cacheworks/Wubbo/KiCad/3d/HRO  TYPE-C-31-M-12.step

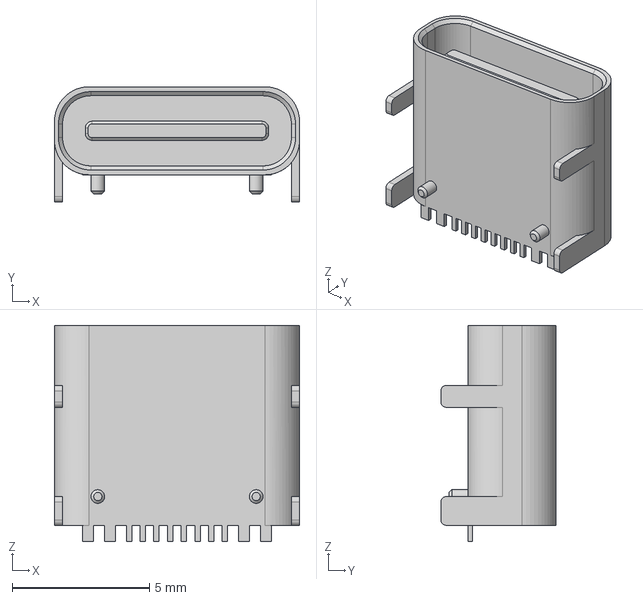
[picture p18: CAD file, 2022-01-12]
KiCad/3d/HRO TYPE-C-31-M-12.step
8.94 x 4.21 x 7.90 mm
