cacheworks/Wubbo/KiCad/3d/USB-C-C168688.step

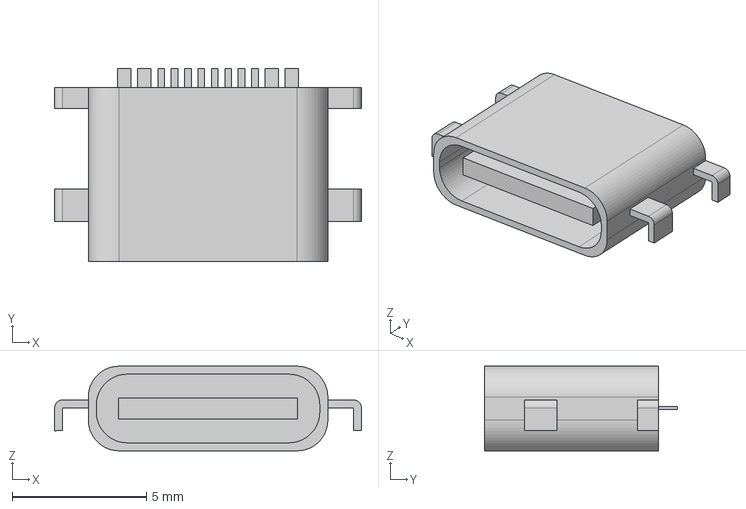
[picture p19: CAD file, 2022-01-12]
KiCad/3d/USB-C-C168688.step
11.5 x 7.20 x 3.16 mm
