cacheworks/Wubbo/KiCad/3d/PG1350-socket.STEP

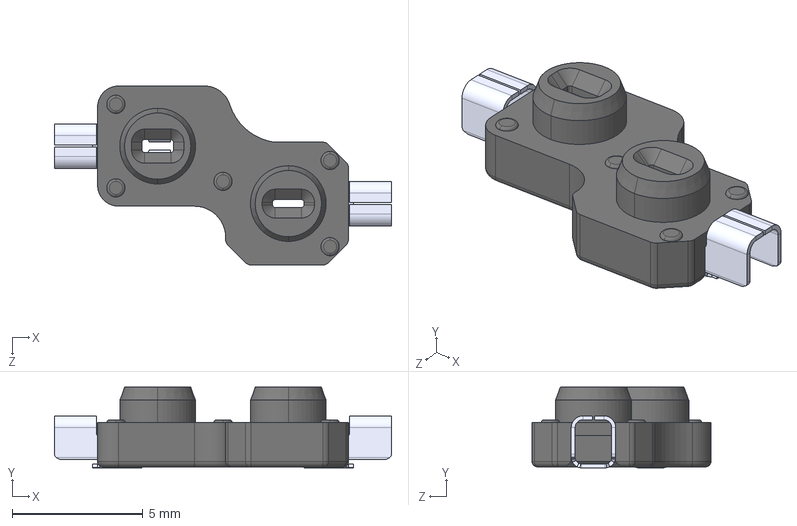
[picture p20: CAD file, 2022-01-12]
KiCad/3d/PG1350-socket.STEP
12.9 x 3.09 x 6.85 mm
pin x 2
socket
