cacheworks/Wubbo/KiCad/3d/LED_SK6812MINI-E.step

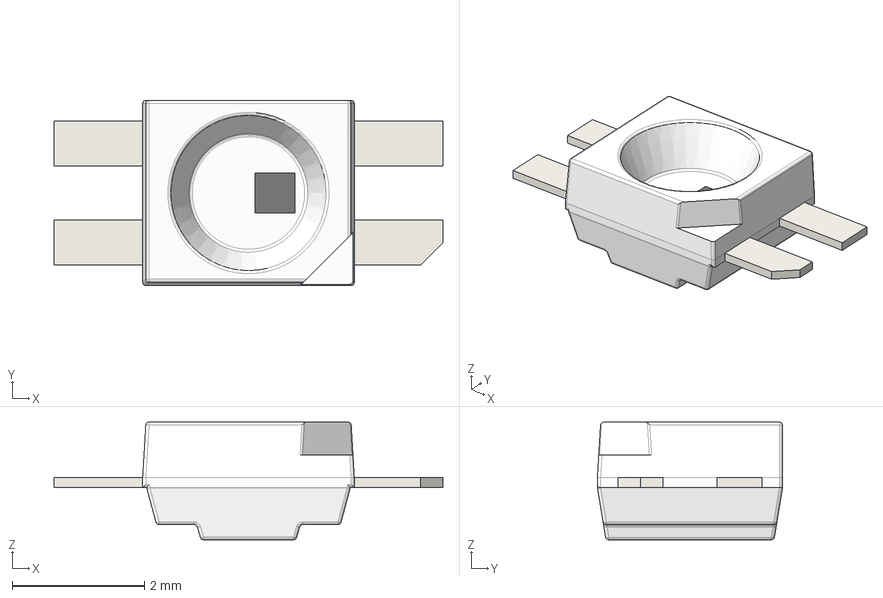
[picture p21: CAD file, 2022-01-12]
KiCad/3d/LED_SK6812MINI-E.step
5.88 x 2.80 x 1.78 mm
