cacheworks/Wubbo/KiCad/3d/ROT_EC11E.step

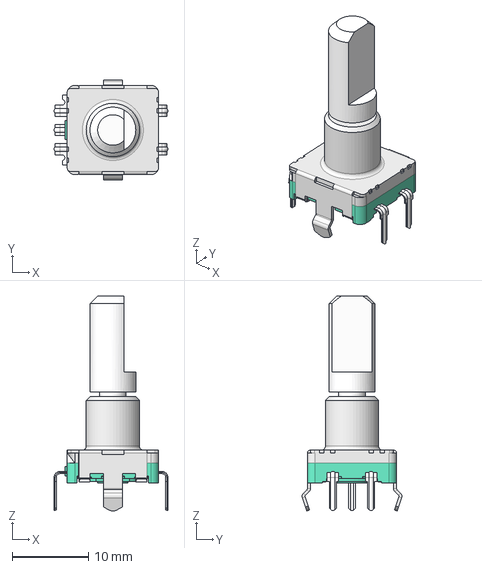
[picture p22: CAD file, 2022-01-12]
KiCad/3d/ROT_EC11E.step
14.9 x 13.1 x 28.2 mm
