cacheworks/Wubbo/KiCad/3d/Stabilizer_Cherry_MX_2u.stp

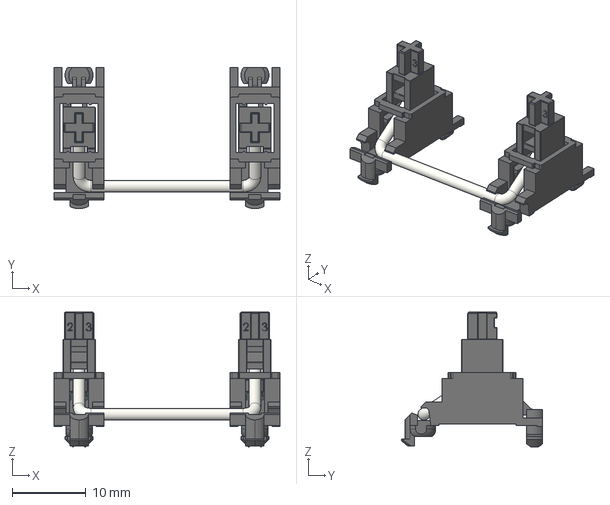
[picture p23: CAD file, 2022-01-12]
KiCad/3d/Stabilizer_Cherry_MX_2u.stp
30.7 x 19.2 x 18.3 mm
