cacheworks/Wubbo/KiCad/3d/Stabilizer_Cherry_MX_6u.stp

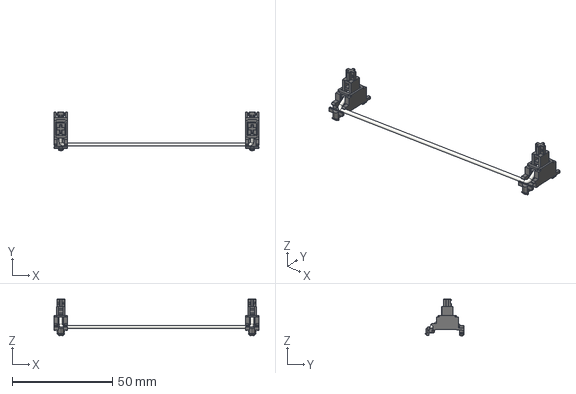
[picture p24: CAD file, 2022-01-12]
KiCad/3d/Stabilizer_Cherry_MX_6u.stp
102.1 x 19.2 x 18.3 mm
