cacheworks/Wubbo/KiCad/3d/SW_Cherry_MX_Plate.stp

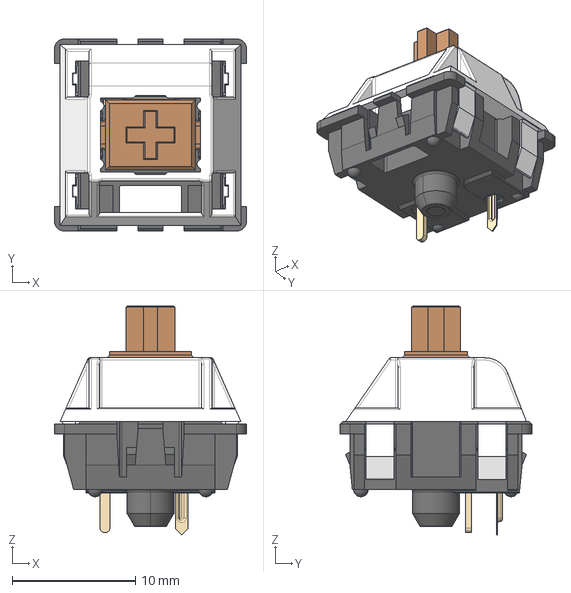
[picture p25: CAD file, 2022-01-12]
KiCad/3d/SW_Cherry_MX_Plate.stp
15.6 x 15.6 x 18.6 mm
