cacheworks/Wubbo/KiCad/3d/CON_Kailh_HS.step

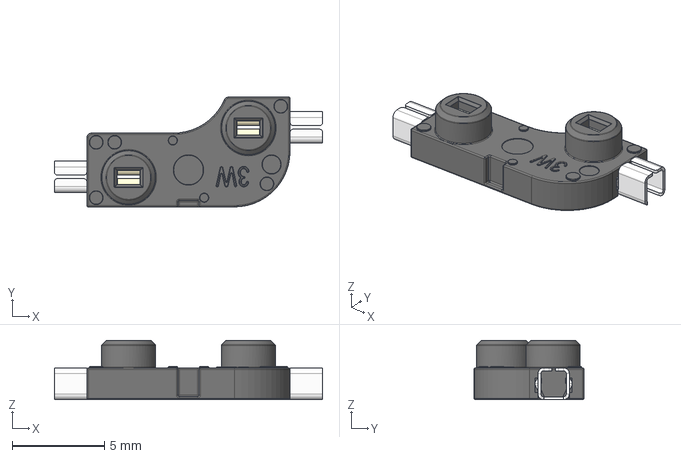
[picture p26: CAD file, 2022-01-12]
KiCad/3d/CON_Kailh_HS.step
14.5 x 5.95 x 3.22 mm
