cacheworks/Wubbo/KiCad/3d/Stabilizer_Cherry_MX_7u.stp

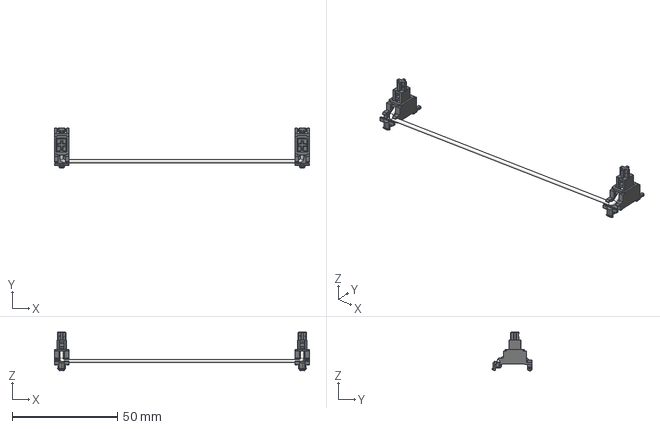
[picture p27: CAD file, 2022-01-12]
KiCad/3d/Stabilizer_Cherry_MX_7u.stp
121.1 x 19.2 x 18.3 mm
