cacheworks/Wubbo/KiCad/3d/Fuse_1206.step

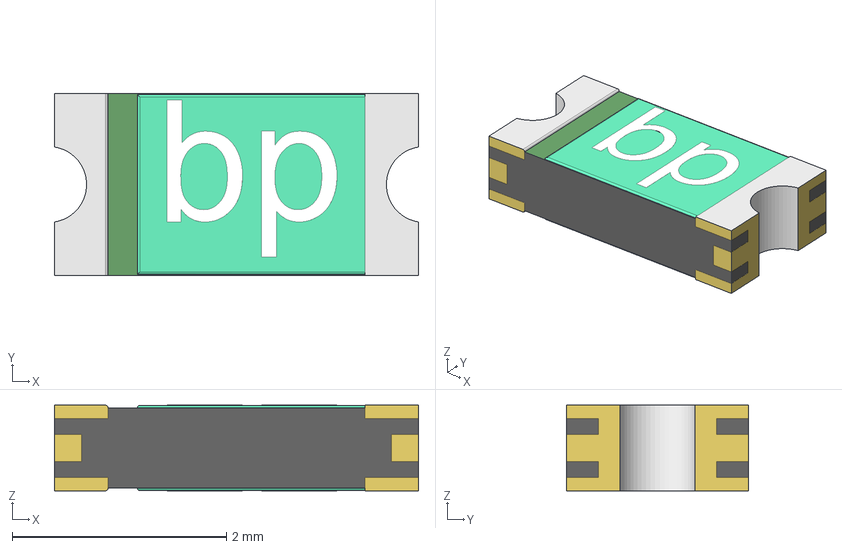
[picture p28: CAD file, 2022-01-12]
KiCad/3d/Fuse_1206.step
3.40 x 1.70 x 0.8 mm
