cacheworks/Wubbo/KiCad/3d/MBK_Keycap_-_1u_Homing.step

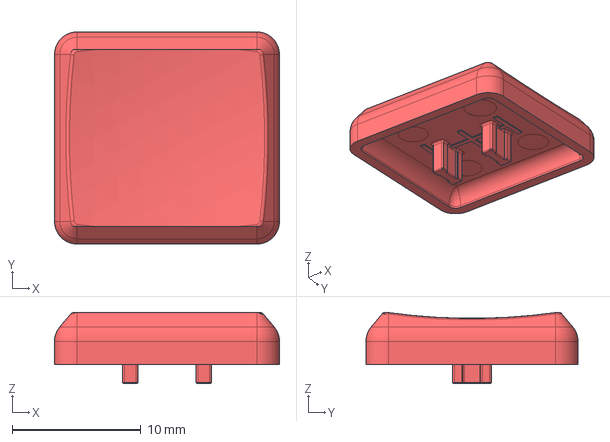
[picture p29: CAD file, 2022-01-12]
KiCad/3d/MBK_Keycap_-_1u_Homing.step
17.5 x 16.4 x 5.54 mm
