cacheworks/Wubbo/KiCad/3d/CON_SM06B-SRSS-TB.step

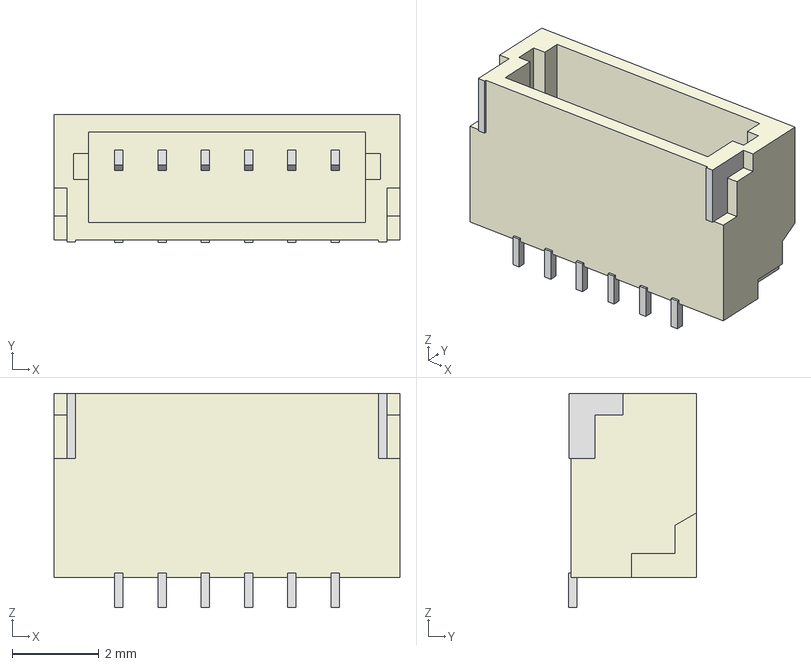
[picture p30: CAD file, 2022-01-12]
KiCad/3d/CON_SM06B-SRSS-TB.step
8.00 x 2.96 x 4.95 mm
