cacheworks/Wubbo/KiCad/3d/SW_Kailh_Choc_V1.stp

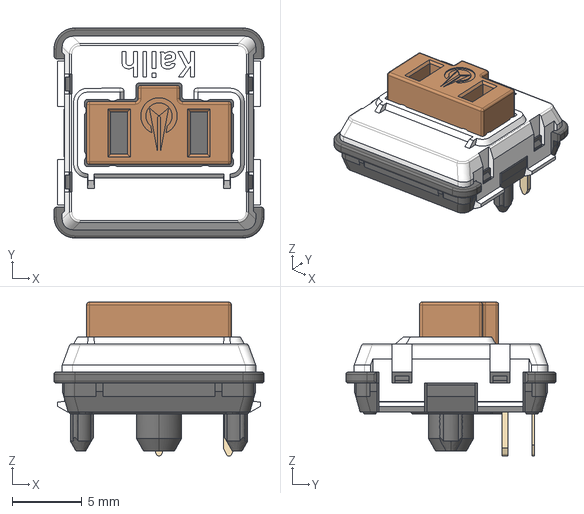
[picture p31: CAD file, 2022-01-12]
KiCad/3d/SW_Kailh_Choc_V1.stp
15.0 x 15.0 x 11.0 mm
