cacheworks/Wubbo/KiCad/3d/CON_SM05B-SRSS-TB.step

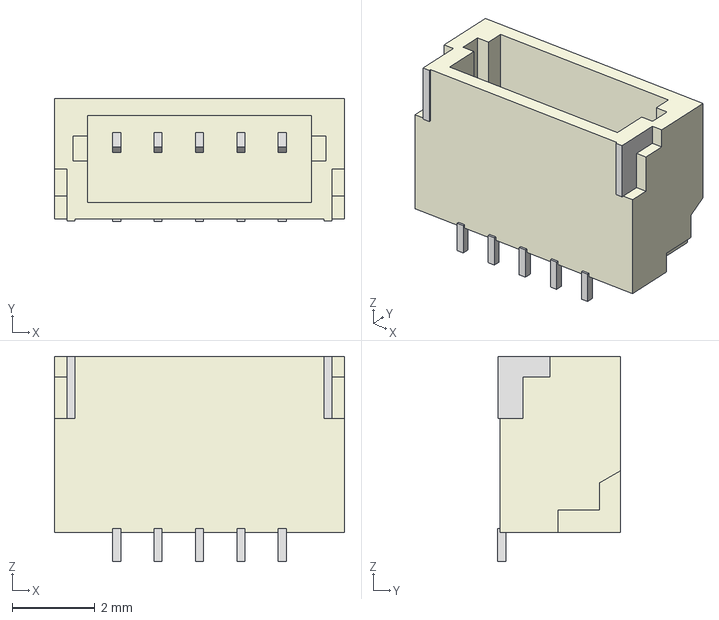
[picture p32: CAD file, 2022-01-12]
KiCad/3d/CON_SM05B-SRSS-TB.step
7.00 x 2.96 x 4.95 mm
