cacheworks/Wubbo/KiCad/3d/CON_TYPE-C-31-M-12.step

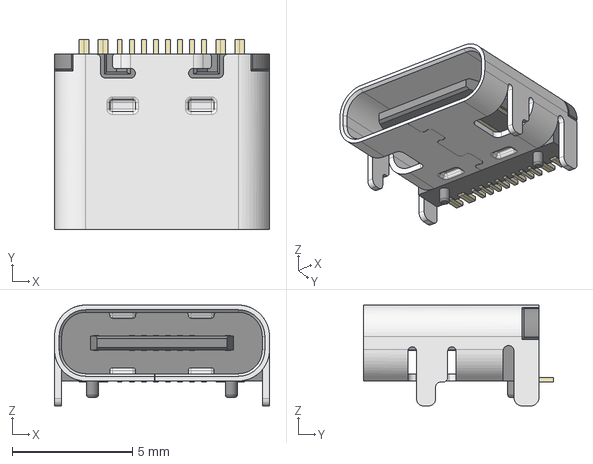
[picture p33: CAD file, 2022-01-12]
KiCad/3d/CON_TYPE-C-31-M-12.step
8.95 x 7.90 x 4.20 mm
