cacheworks/Wubbo/KiCad/3d/Stabilizer_Cherry_MX_3u.stp

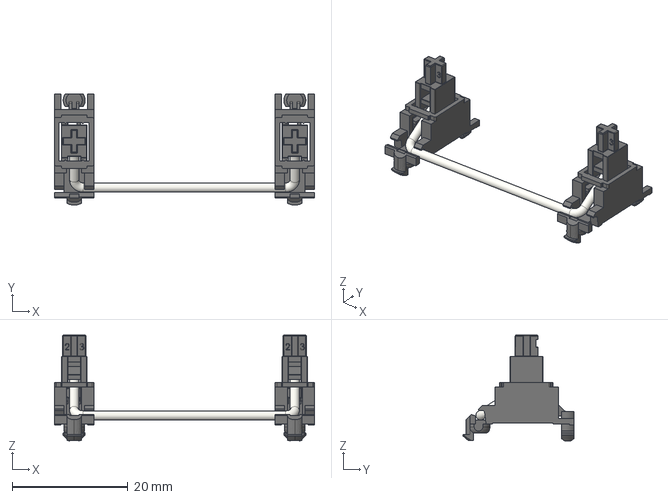
[picture p34: CAD file, 2022-01-12]
KiCad/3d/Stabilizer_Cherry_MX_3u.stp
44.9 x 19.2 x 18.3 mm
