cacheworks/Wubbo/KiCad/3d/LED_WS2812B-MINI.step

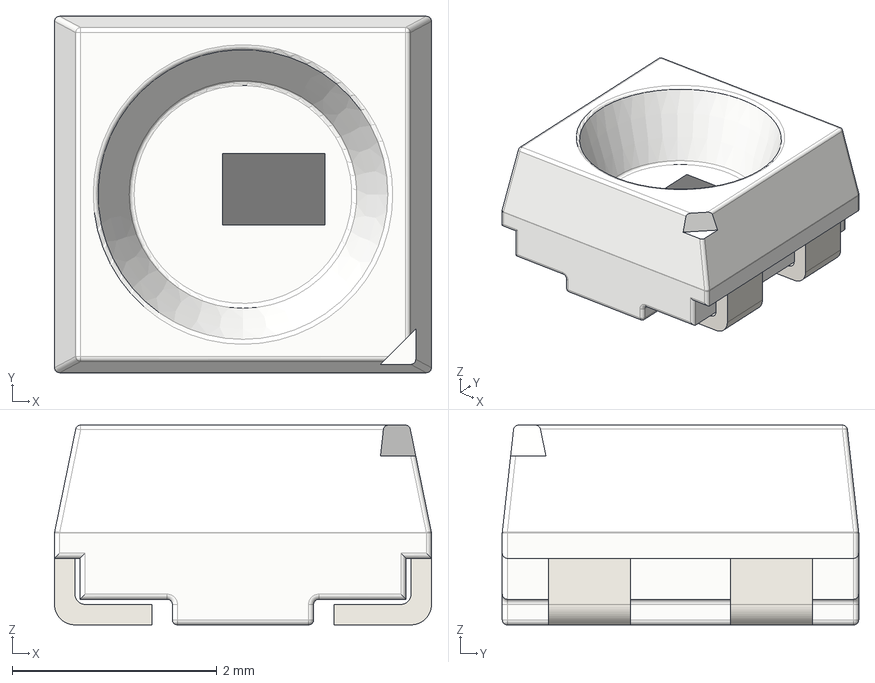
[picture p35: CAD file, 2022-01-12]
KiCad/3d/LED_WS2812B-MINI.step
3.68 x 3.48 x 1.95 mm
