cacheworks/Wubbo/KiCad/3d/CON_SM08B-SRSS-TB.step

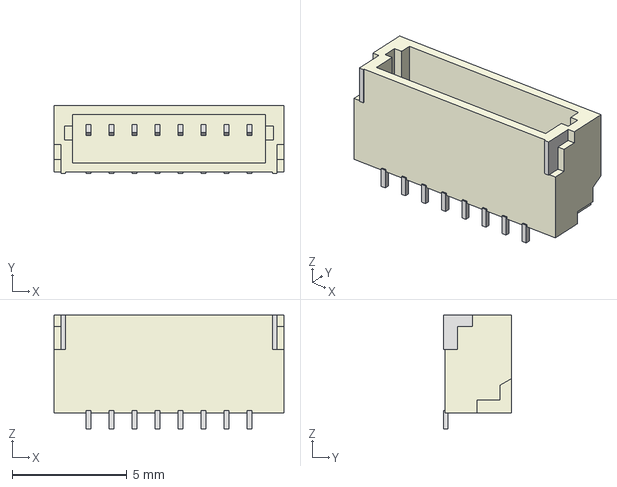
[picture p36: CAD file, 2022-01-12]
KiCad/3d/CON_SM08B-SRSS-TB.step
10.0 x 2.96 x 4.95 mm
