cacheworks/Wubbo/KiCad/3d/MBK_Keycap_-_1.5u.step

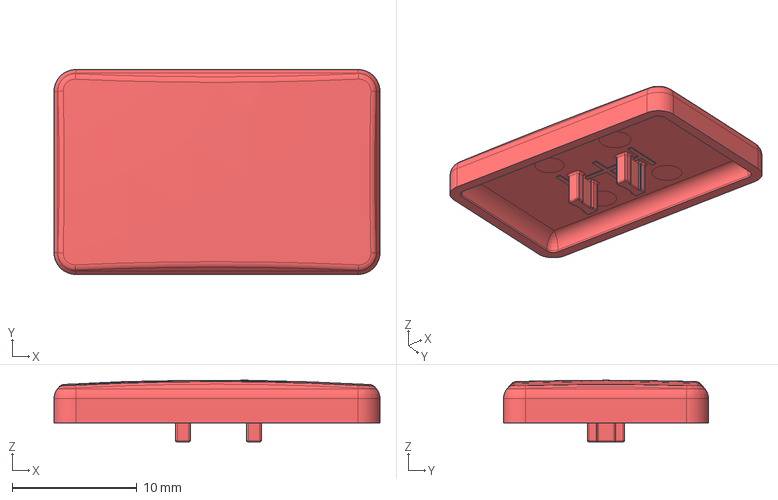
[picture p37: CAD file, 2022-01-12]
KiCad/3d/MBK_Keycap_-_1.5u.step
26.2 x 16.4 x 4.94 mm
